yarda/flasher/flasher.kicad_sch

## KiCad design flasher.kicad_sch (2023-01-22)

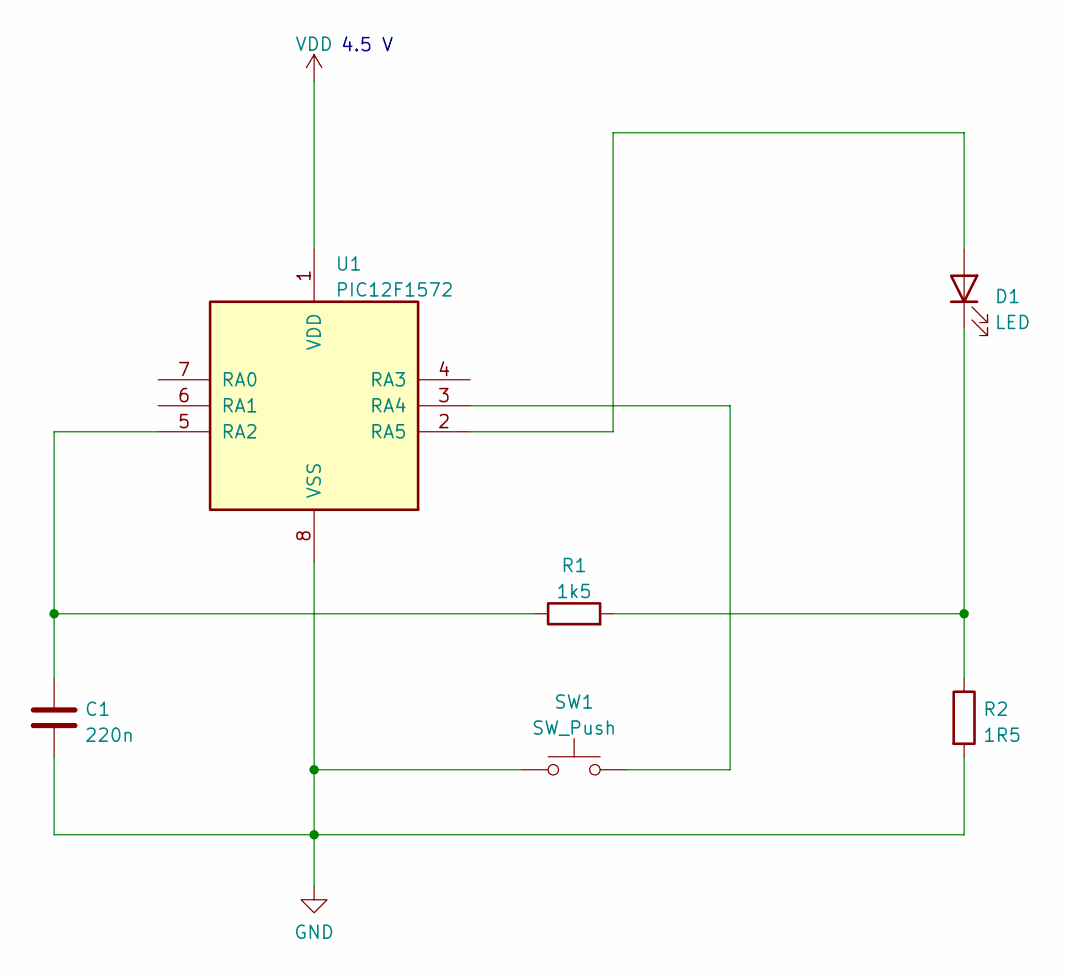
[picture p3: schematic flasher.kicad_sch]

Parts:
C1: 220n
D1: LED
R1: 1k5
R2: 1R5
SW1: SW_Push
U1: PIC12F1572; DIP-8_W7.62mm

Connections:
GND: C1.2, R2.2, SW1.1, U1.8 (VSS)
unnamed: C1.1, R1.1, U1.5 (RA2)
unnamed: D1.1 (K), R1.2, R2.1
unnamed: D1.2 (A), U1.2 (RA5)
unnamed: SW1.2, U1.3 (RA4)
VDD: U1.1 (VDD)

Notes on the sheet:
4.5 V
